samuelgbrown/BikeLights_Arduino/Bike_Lights_refined_bb.png

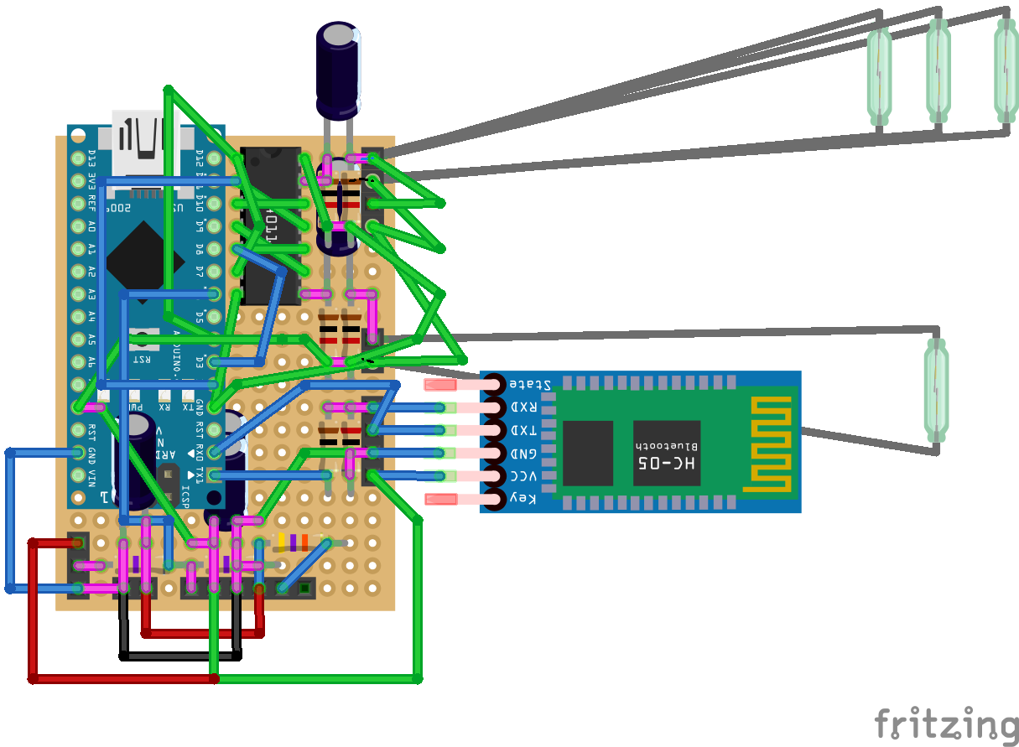
Bike_Lights_refined_bb.png
