samuelgbrown/BikeLights_Arduino/pics/Main Case 01.jpg

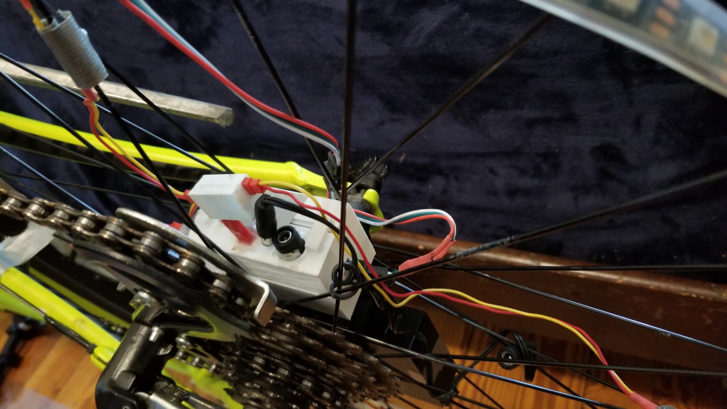
pics/Main Case 01.jpg
