samuelgbrown/BikeLights_Arduino/pics/Main Case 2.jpg

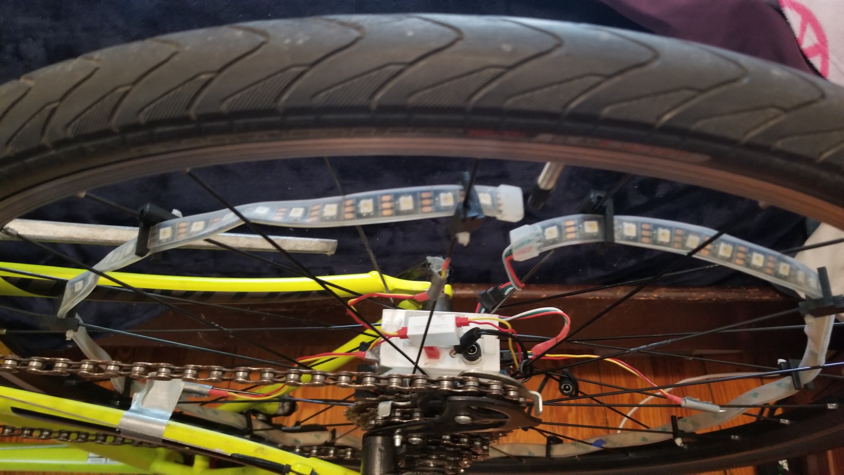
pics/Main Case 2.jpg
