samuelgbrown/BikeLights_Arduino/include/Pattern.h

/*

  The Pattern object is responsible for generating the LED pattern displayed to the wheel.  Its input is the position, velocity, and acceleration of the "reference point" on the LED strip.
  The "reference point" is a value from [0 NUMLEDS) that represents which LED is at the top of the wheel at any given point in time.

  The Pattern_Handler object is responsible for loading Patterns, allowing the user to swap out different patterns at will.
  It also calls main and idle animations independently, allowing the user to chose main and idle animations individually.

  If the speed of the wheel falls under some threshold, it will be assumed that program no longer has a good guess of where the reference point is, so an "idling animation" will begin,
  an animation which plays when the wheel is Still or moving slowly that does not rely on the location of the reference point.

  Samuel G. Brown
  July 28 2017

*/

#ifndef Pattern_h
#define Pattern_h

#include "Arduino.h"
#include "Definitions.h"
#include "Speedometer.h"
#include "Color.h"
#include <math.h>

#if !NO_BLUETOOTH
#include "Bluetooth.h"
#endif

class Image_Helper; 
class btSerialWrapper;

// Each Pattern holds on to an array of Color_'s (abstract color objects which may be static or dynamic without input needed from the Pattern), and an "image" array that maps each LED on the wheel to a Color_
class Pattern
{
public:
  Pattern(Pattern_Handler* parent_handler);                                              // Constructor
  Pattern(Pattern_Handler* parent_handler, Image_Helper *image_helper, boolean groundRel); // Constructor

  // Pattern(Color_ **colorsIn, unsigned char numColorsIn); // Constructor

  virtual ~Pattern(); // Destructor

  virtual void anim(float xTrue); // Animation function
  void anim() { anim(0); };            // Define a parameter-less call to anim to be the same as claiming that the x position is always 0

  // // Functions to manage the "palette" array of Color_**'s, or the Color_'s that this pattern may show
  // void setupPalette(unsigned char numColors);
  // void setupPalette(Color_ **colorsIn, unsigned char numColorsIn);
  // void setColor(Color_ *newColor, unsigned char colorNum); // Set a color in the specified location

  // unsigned char getNumColors(); // Get the number of palette currently assigned to this pattern

  // Functions to manage the "image", or the LED map which shows which LEDs are showing which Color_
  void setImage(unsigned char *image);               // Set an image to the pattern
  void setImageFromBluetooth(btSerialWrapper * btSer); // Set the image to the Pattern, by reading data directly from the bluetooth data stream
  // void setImageValInPos(unsigned char LEDNum); // Set an image value in a specific LED location
  // void setImage(uint32_t *image);      // Set an image to the pattern
  // void setImageColorInd(unsigned char colorInd); // Set the image as all references to a single color
  // void setImageNumSegs(unsigned char numSegs);   // Set some number of equally spaced dots on the image

  unsigned char getImageValInPos(unsigned char LEDNum); // Get the value of image at the specified location
  unsigned char getImageRawByte(unsigned char byteNum); // Get the raw byte value in image at the specified location
  const unsigned char *getImage() const;                // Get a pointer to the image

  // Function for encoding information to Android
  // virtual ImageMeta_BT getImageType(); // Get the type of image represented by this Pattern, and its related information (default is a constant with 0 rotational speed)

  unsigned char getImageType() const;     // Get the type of Image that is being used
  bool supportIdle() const;               // Does this Pattern support an idle animation?
  signed char getHelperParameter() const; // Get the parameter for the Image_Helper assigned to this Pattern

private:
  bool groundRel;                          // Should the Pattern be calculated relative to the ground, or relative to the wheel (i.e. if ground-relative, a non-moving image will appear still from a person standing on the street.  If wheel-relative, a non-moving image will appear to rotate at the same rate as the wheel)
  Pattern_Handler *parent_handler;                // A pointer to the parent pattern_handler, used to get access to the color palette
  unsigned char image[NUM_BYTES_PER_IMAGE] = {0}; // The image that will be painted onto the wheel, using the palette provided by Pattern_Handler.  Defined as an array of integers, each of which represents a "color index", or the index in the palette array that represents the color desired (initialized to 0's) // TODO: Update
  // unsigned char * image = new unsigned char [NUM_BYTES_PER_IMAGE]; // The image that will be painted onto the wheel, using the palette provided by Pattern_Handler.  Defined as an array of integers, each of which represents a "color index", or the index in the palette array that represents the color desired (initialized to 0's)
  Image_Helper *image_helper = NULL;              // The Image_Helper for this Pattern, which defines how the image moves

  void sendLEDsWithOffset(int offset);                // Function to send the image to the LED strip, using some LED offset calculated by the Image_Helper (and the wheel position, if displaying the image relative to the ground)
  void setImageHelper(Image_Helper *image_helper_in); // Function to set the Image_Helper
};

// Object that holds onto and manages each pattern currently instantiated (one main, and one idle)
class Pattern_Handler
{
public:
  Pattern_Handler(Speedometer *speedometer);                                               // Constructor
  Pattern_Handler(Speedometer *speedometer, Color_ **colorsIn, unsigned char numColorsIn); // Constructor
  ~Pattern_Handler();                                                                      // Destructor

  void mainLoop(); // Main function that executes every loop

  void setMainPattern(Pattern *newMainPattern); // Set the main pattern
  void setIdlePattern(Pattern *newIdlePattern); // Set the idle pattern

  void deletePatterns(); // Delete the image patterns that this handler is currently holding onto
  
  void setPowerState(bool newPowerState); // Set the power state of the wheel
  bool getPowerState();                   // Get the power state of the wheel

  const Pattern *getMainPattern(); // Get a const pointer to the main Pattern
  const Pattern *getIdlePattern(); // Get a const pointer to the main Pattern

  // Functions to manage the "palette" array of Color_**'s, or the Color_'s that this pattern may show
  unsigned char getNumColors(); // Get the number of palette currently assigned to this pattern

  void setupPalette(unsigned char numColors);
  void setupPalette(Color_ **colorsIn, unsigned char numColorsIn);

#if USE_NANOPB
  void setupPalette(Color_BT *colorMessagesIn, unsigned char numColorsIn);
#endif

  void setColor(Color_ *newColor, unsigned char colorNum); // Set a Color_ in the specified location
  const Color_ *getColor(unsigned char colorNum);          // Get a pointer to the Color_ at the specified location
  unsigned char numColors = 0;                                 // The number of palette is defaulted to 0 (Max of 16 Color_'s)

  void setBrightnessFactor(float newBrightnessFactor); // Set the brightnessFactor
  float getBrightnessFactor();                         // Get the brightness factor

  void preCalculateAllColor_();                                // Pre-calculate all colorObj's from each Color_ being used this loop
  colorObj getPreCalculatedColorInPos(unsigned char colorNum); // Get a specific colorObj according to its position in palette (If using this function, MUST have run preCalculateAllColor_() earlier in the loop)

private:
  // Speedometer pointer (kept to pass on to new Patterns)
  Speedometer *speedometer = NULL; // Speedometer (used to retrieve the pos/vel/acc of the wheel), DO NOT ATTEMPT TO DELETE

  // Pattern pointers
  Pattern *mainPattern = NULL; // The main pattern
  Pattern *idlePattern = NULL; // The idle pattern

  // Color_ functions and information
  void deleteColorArray();              // Delete the array palette and its contents
  Color_ **palette = NULL;              // Array of Color_ objects
  colorObj *preCalculatedColors = NULL; // Array (of size numColors) of colorObj's that represents the colorObj for each Color_ represented in image that is being used this loop (each Color_ is calculated only once, so computation time will be saved on dynamic palette).
  float brightnessFactor = 1.0f;        // A scale factor to adjust the brightness each time the colors are precalculated (can be used to homogenously dim the LEDs)
  bool mainAllowsIdle = false;          // Does the main Pattern allow an idle Pattern?

  // Power state
  bool powerState = true;            // The power state of the LED (should the LED's be turned on? True = on)
  bool powerStateChangedOff = false; // Has the powerstate recently been changed?
};

// An abstract helper class that defines the single function that all helpers must return, the current offset of the pattern's rotation.  It allows the derived classes to change how the image moves around the wheel (either relative to the ground, or relative to the wheel)
class Image_Helper
{
public:
  Image_Helper(bool idleAllowed = true);

  virtual ~Image_Helper() {}; // Default (virtual) destructor

  virtual float getHelperOffset(float xTrue) = 0; // Returns the image offset defined by this image helper.  Called once per loop, it must perform all necessary calculations to updating and returning the offset value
  bool isIdleAllowed();
  virtual IMAGE_HELPER_TYPE getType() = 0;
  virtual signed char getHelperParameter() = 0; // Get the parameter information for this Helper (can be expanded later on by making it into 2 functions: one to return the number of bytes required to encode the data, and another to assign the data to an array that will be assigned to a pointer passed to the function)

private:
  bool idleAllowed = true; // Does this Image_Helper generate a Pattern that allows an idle animation?  Derived classes must overwrite this if they do not allow idle animations (such as the Spinner)
  // TODO: If implementing color blurring with SRAM, may need to have another function that can affect the colors themselves somehow
};

// A helper class to describe Patterns whose images do not move over time
class Static_Helper : public Image_Helper
{
public:
  Static_Helper();
  IMAGE_HELPER_TYPE getType() { return STATIC; } // Static image helper
  signed char getHelperParameter();

  float getHelperOffset(float xTrue); // Always returns a 0, because the image should not move
};

// A helper class to describe Patterns that use a moving image
// TODO: Improve the documentation and naming of the variables in here; blurring may become viable if I use SRAM, and I'm never going to get it to work if I have no idea what any of this stuff does.
class Moving_Helper : public Image_Helper
{
public:
  // Class specific functions
  Moving_Helper();
  Moving_Helper(signed char rotateSpeed);

  IMAGE_HELPER_TYPE getType() { return MOVING; } // Moving image helper
  signed char getHelperParameter();

  void setRotateSpeed(signed char rotateSpeedIn); // Change rotateSpeed
  int getRotateSpeed();                           // Get the rotation speed

  // Image_Helper function
  float getHelperOffset(float xTrue); // Return the current image position

  // Functions that require SRAM
#if SRAM_ATTACHED
  Moving_Helper(int rotateSpeed, unsigned char imageBleed);
  void setImageBleed(unsigned char imageBleedIn);                          // Change imageBleed
  void addImagePosition(colorObj colorObjIn, unsigned char imagePosition); // (Bit of a weird one...) For use during the anim_preImagePosUpdate() loop in derived classes.  Replaces adding a colorObj to the controller::sendPixel() function, instead sending the pixel to this object's colorMemory buffer for further processing (offsetting by imageMovementPos and "blurring")

protected:
  colorObj colorMemory[NUMLEDS]; // TODO: Update this so it changes with new values of numLEDs from Android!!! An array of colorObj's that keeps track of the history of movements
#endif

private:
  signed char rotateSpeed = 10;                // Speed of image rotation (in LEDs/second)
  float imageMovementPos = 0;                  // Current image reference position around the wheel
  unsigned long lastLEDAdvanceTime = micros(); // The time at which imageMovementPos was last updated

  void advanceLEDPos(); // Advance the current location of the image reference position around the wheel

#if SRAM_ATTACHED
  unsigned char imageBleed = 150; // Amount of "bleed" from the moving image (0 <= bleedIn <= 255, higher values mean more after-image)

  void colorBlur();  // Calculate the blurring of the color memory
  void sendColors(); // Send the palette in colorMemory to the LEDs

#endif
};

class Spinner_Helper : public Image_Helper
{
public:
  Spinner_Helper();                    // Constructor
  Spinner_Helper(signed char inertia); // Constructor

  IMAGE_HELPER_TYPE getType() { return SPINNER; } // Spinner image helper
  signed char getHelperParameter();

  void setInertia(signed char inertiaIn); // Change inertia
  unsigned char getInertia();             // Get the inertia

  // TODO: Complete this Image_Helper!!!
  // Image_Helper function
  float getHelperOffset(float xTrue); // Return the current image position

private:
  signed char inertia = 10;                    // The inertia that the Spinner has
  float imageMovementPos = 0;                  // Current image reference position around the wheel
  float imageMovementVel = 0;                  // Current image reference velocity around the wheel
  unsigned long lastLEDAdvanceTime = micros(); // The time at which imageMovementPos was last updated
  float lastTrueXPosition = 0;                   // The last x position of the wheel (used to calculate the wheel's current true speed)

  void advanceLEDPos(float xTrueRounded); // Advance the current location of the image reference position around the wheel
};

// // A main animation that features an image that appears to not rotate relative to the ground
// class Still_Image_Main : public Pattern_Main
// {
// public:
//   Still_Image_Main(Speedometer *speedometer, unsigned char *image); // Constructor
//   Still_Image_Main(Speedometer *speedometer);                       // Constructor

//   void anim(); // Main animation function
// };

// // A main animation that features an image that appears to rotates at a set speed relative to the ground
// class Moving_Helper_Main : public Still_Image_Main, public Moving_Helper
// {
// public:
//   Moving_Helper_Main(Speedometer *speedometer, unsigned char *image); // Constructor
//   Moving_Helper_Main(Speedometer *speedometer);                       // Constructor

//   ImageMeta_BT getImageType();

//   void anim_preImagePosUpdate(int xTrueRounded); // Main animation function
//   void anim() { Moving_Helper::anim(); };         // Redefine anim() to be the Moving_Helper anim()
// };

// // An idle animation that features an image that does not rotate relative to the wheel
// class Still_Image_Idle : public Pattern_Idle
// {
// public:
//   Still_Image_Idle(unsigned char *image); // Constructor
//   Still_Image_Idle();                     // Constructor
//   void anim();                            // Idle animation function

// private:
//   // Blink class leftovers
//   //    unsigned long timeAtToggle = 0;
//   //    unsigned long timeOff = 200;
//   //    unsigned long timeOn = 800;
//   //
//   //    //    unsigned char idleBrightness = 0;
//   //    boolean idleToggleSig = false;
// };

// // An idle animation that features an image that rotates relative to the wheel
// class Moving_Helper_Idle : public Still_Image_Idle, public Moving_Helper
// {
// public:
//   Moving_Helper_Idle(unsigned char *image); // Constructor
//   Moving_Helper_Idle();                     // Constructor

//   ImageMeta_BT getImageType();

//   void anim_preImagePosUpdate(int xTrueRounded); // Idle animation function
//   void anim() { Moving_Helper::anim(); };         // Redefine anim() to be the Moving_Helper anim()
// };

// A class in charge of communicating with the LED strip
class controller
{
public:
  // Public functions that are needed by other objects
  static void sendPixel(unsigned char r, unsigned char g, unsigned char b, unsigned char w); // Load a single pixel onto the LED strip (first LED in strip receives first color loaded)
  static void sendPixel(Color_ *colorIn);                                                    // Load a single pixel onto the LED string (same as above, using a Color_ object instead of unsigned char values)
  static void sendPixel(colorObj colorObjIn);                                                // Load a single pixel onto the LED string (same as above, using a colorObj object instead of unsigned char values or a Color_ object)
  static void show_LEDs();                                                                   // Display the pattern that was just loaded onto the NUMLEDS number of pixels using sendPixel()
  static void ledsetup();                                                                    // Set up the Arduino for low-level communication with the LED strip

private:
  // Low-level communication with the LED strip
  static void sendBit(bool bitVal);         // Send a bit to the LED string
  static void sendByte(unsigned char byte); // Send a byte to the LED string, represents brightness of a single-colored LED
};
#endif
